Herotech1105/Anwendungsprojekt.Inf/documentation/Phase_4/API_Phase_4_Lennart_Esch.pdf

# Phase 4

# Storing Censor Data in Database (Lennart Esch)

Barnabas Steiner - Benjamin Hager - Jannis Weber - Lennart Esch - Tim Dorozynski - Walter Neer

# Agenda

# 1. Problemstellung 2. Deployment 3. Aufgaben 4. Controller 5. NGINX 6. WebServer 7. MariaDB 8. Zusammenspiel

# Problemstellung

# - Datentransfer

# - MQTT-Broker -> Datenbank - Sichere Übertragung

# - Kommunikation

# - PICO <-> Controller

# Deployment

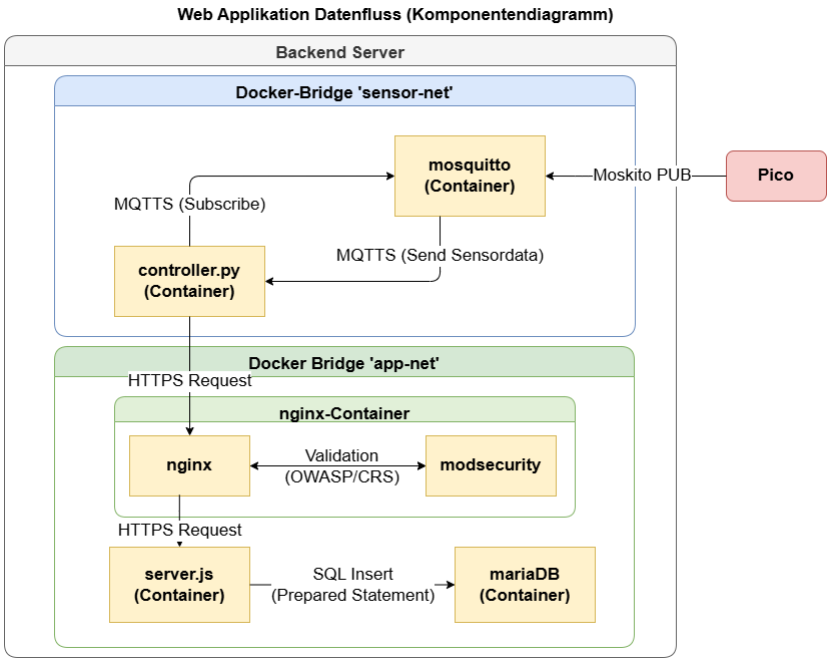
[picture p68: figure]

# Deployment

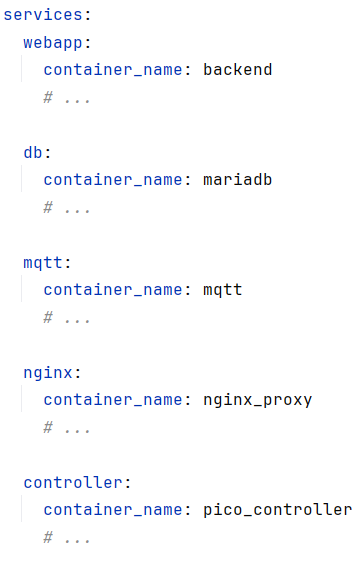
[picture p69: figure]

# - Mittels docker-compose.yml

# Aufgaben


# Controller

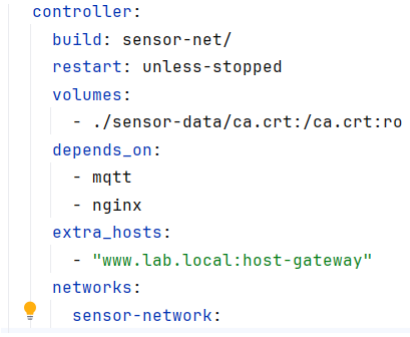
[picture p70: figure]

# - Python Script - Image gebaut durch Dockerfile - Dateizugriff auf Zertifikat - HTTPS Zugriff auf host-system

# Controller

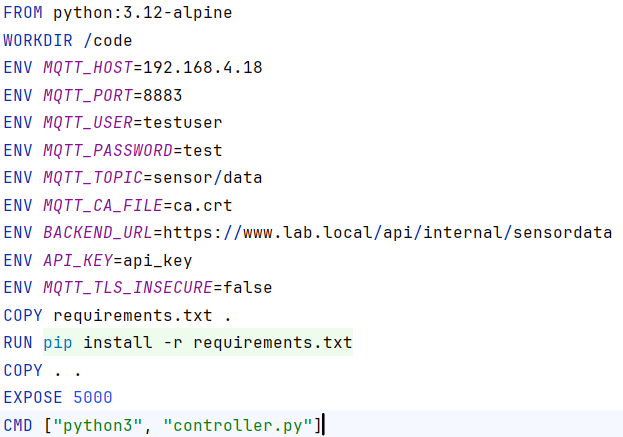
[picture p71: figure]

# - Basierend auf Python 3.12 Image - Umgebungsvariablen für das Skript - Installation aus requirements.txt

# - Paho_mqtt - Requests

# Controller

# - Client aus paho_mqtt

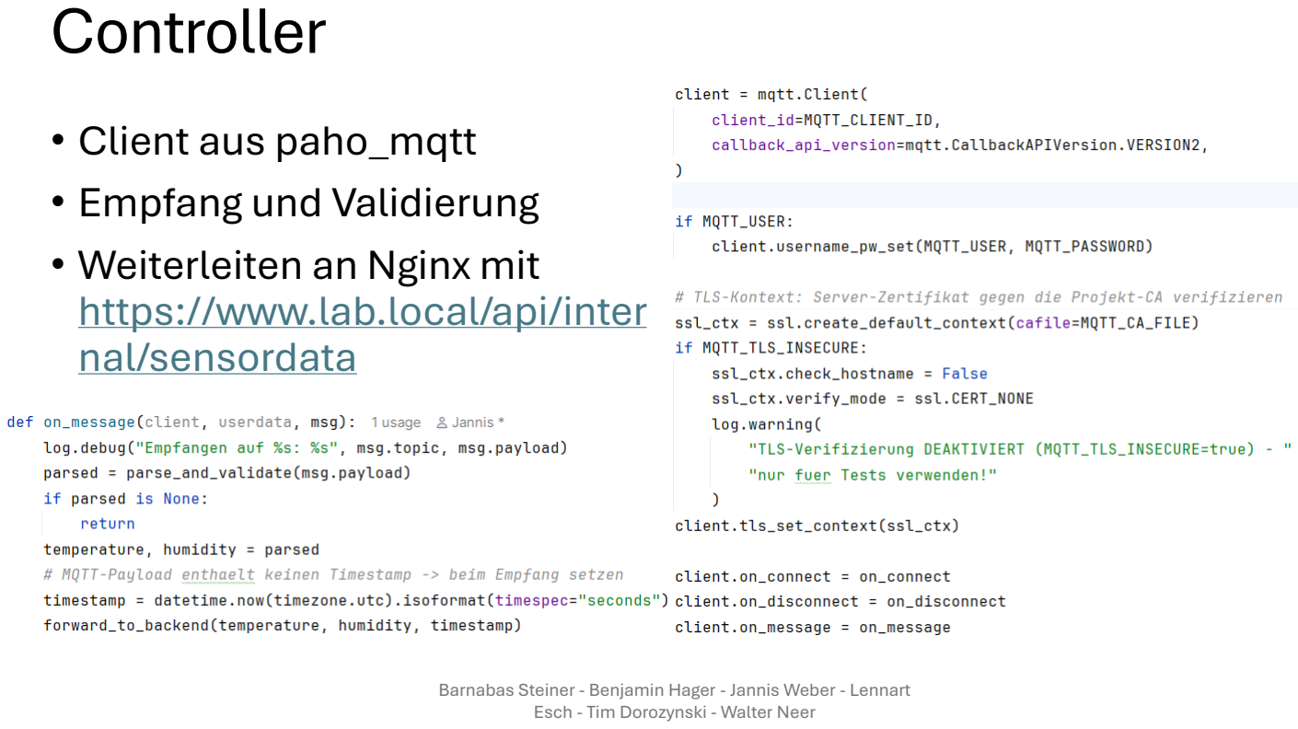
[picture p72: page 9]

# - Empfang und Validierung - Weiterleiten an Nginx mit https://www.lab.local/api/inter nal/sensordata (https://www.lab.local/api/internal/sensordata)

# Nginx

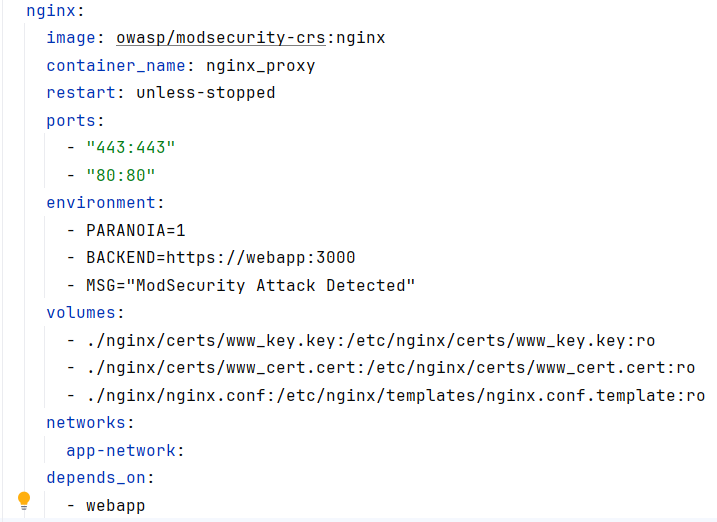
[picture p73: figure]

# - OWASP-Image

# - SQL Injection - XSS - Directory Traversal

# - HTTP/HTTPS Ports geöffnet - Niedrige Sicherheitsstufe - Zugriff auf Zertifikate

# Nginx

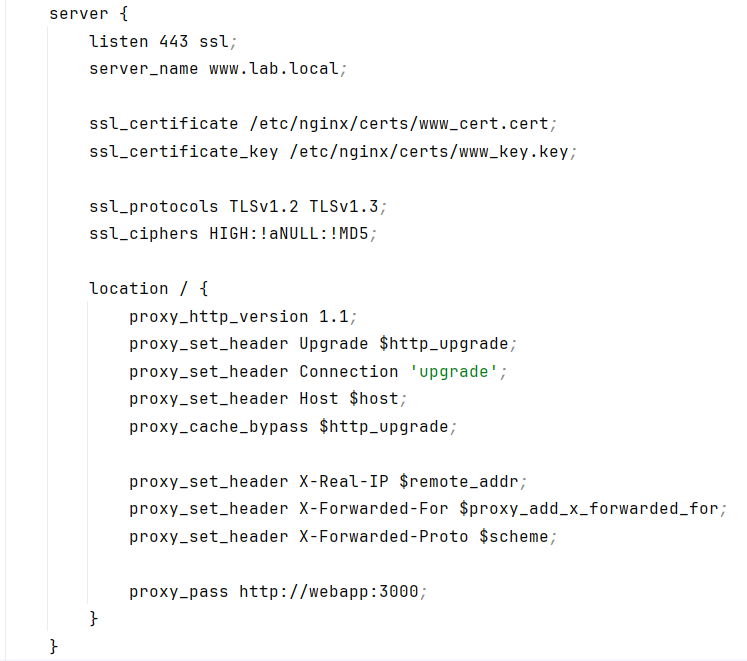
[picture p74: figure]

# - HTTPS Weiterleitung auf webapp - Selbsterstellte Zertifikate

# Webserver

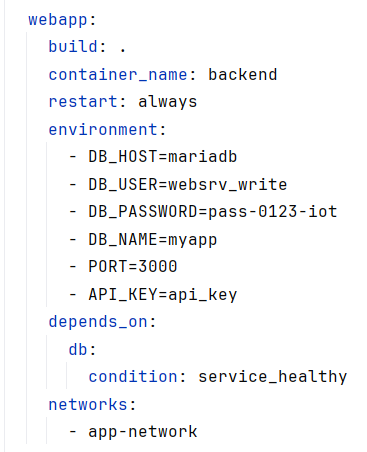
[picture p75: figure]

# - Node/Express server - Image gebaut aus Dockerfile - Datenbank Credentials - Api-Key

# Webserver

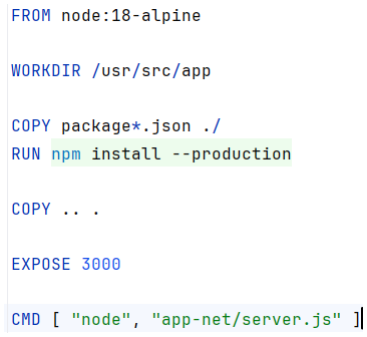
[picture p76: figure]

# - Basiert auf Node-Image - Installiert mit package.json

# - Express - Dotenv - MariaDB

# - Läuft intern auf 3000

# Webserver

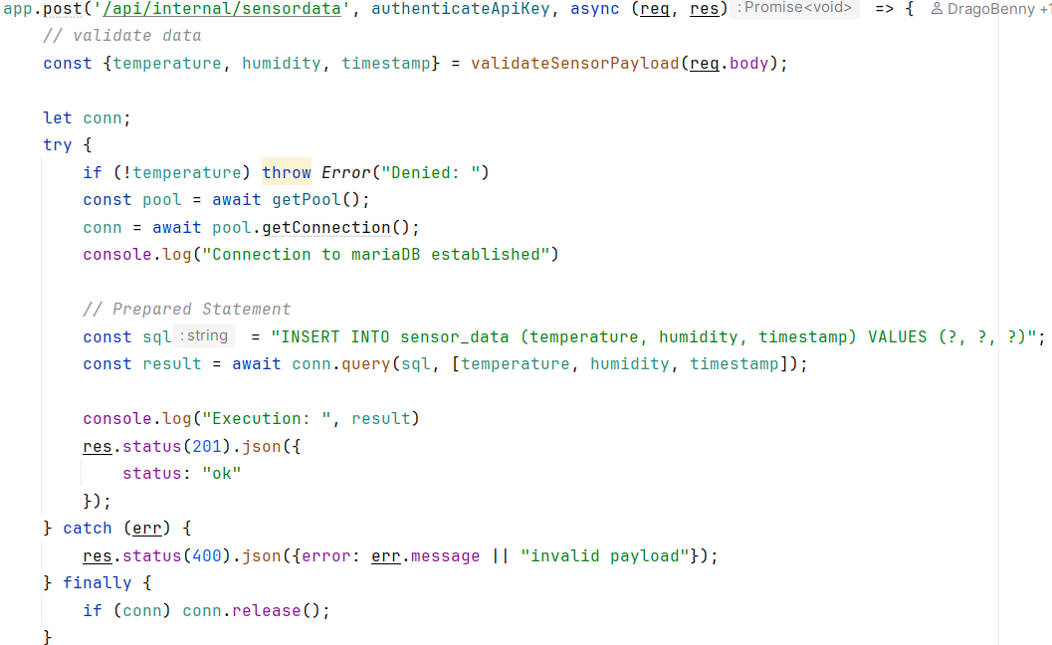
[picture p77: figure]

# MariaDB

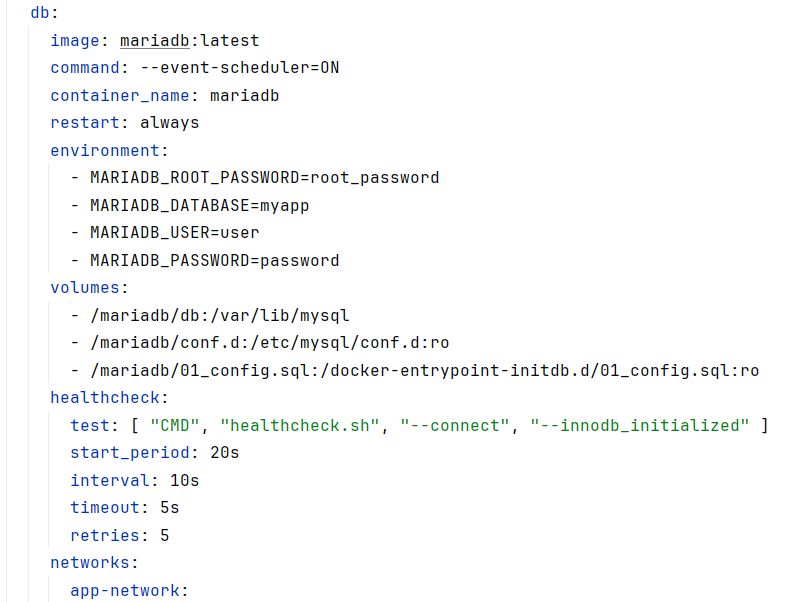
[picture p78: figure]

# - Event Scheduler - Credentials - Persistenz - Healthcheck

# MariaDB

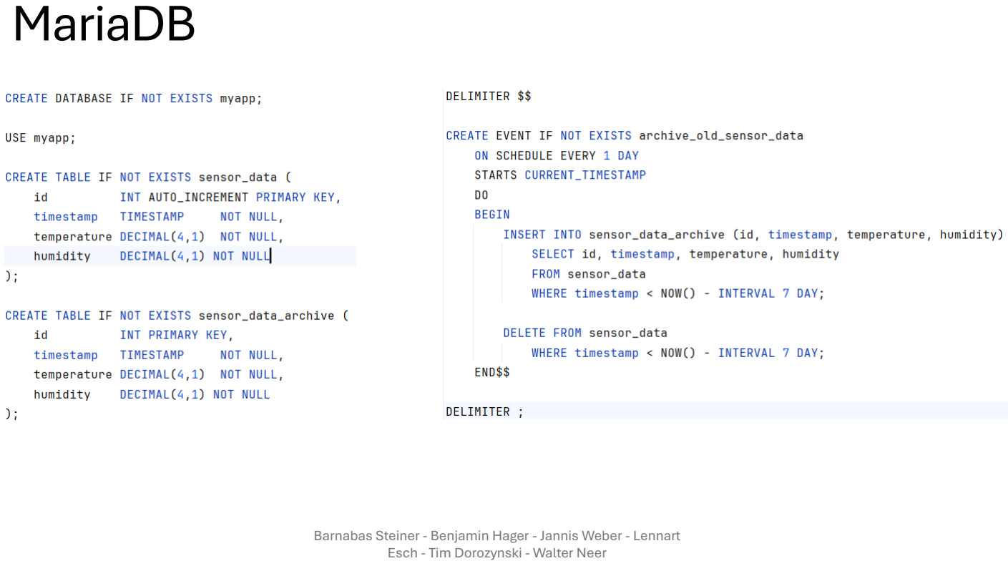
[picture p79: page 16]

# Zusammenspiel

# - E2E Test

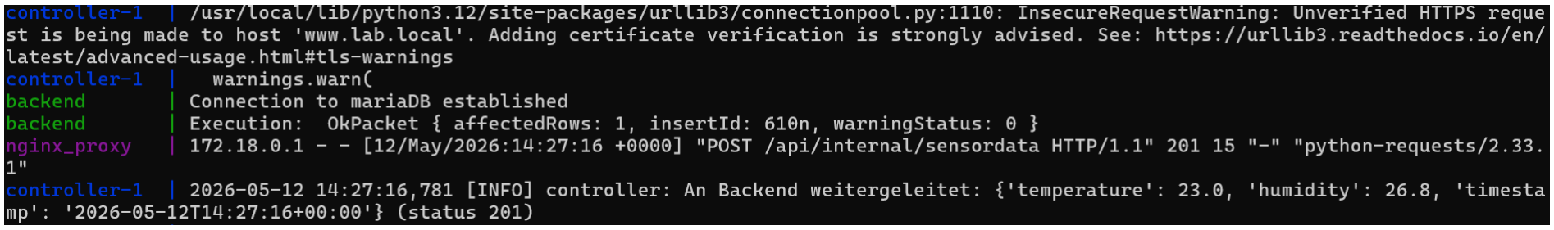
[picture p80: figure]

# - Warnung Zertifikat Nginx - Datenbank Query Ausführung - Response Code 201 an Controller

# Zusammenspiel

# - Verbindung mit MariaDB

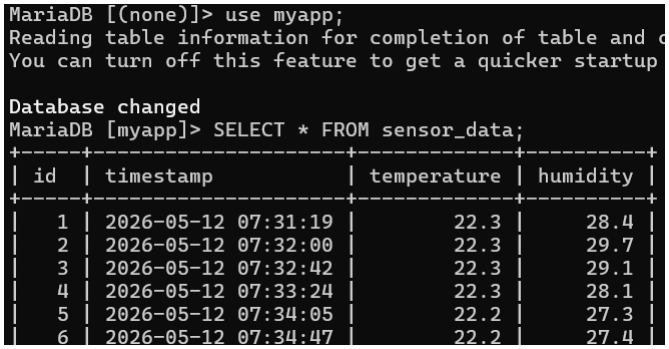
[picture p81: figure]

# - Database myapp - Sensor Data wird gefüllt

# Vielen Dank für Ihre Aufmerksamkeit
