Herotech1105/Anwendungsprojekt.Inf/documentation/Phase_1/Gantt_Phase1.pdf

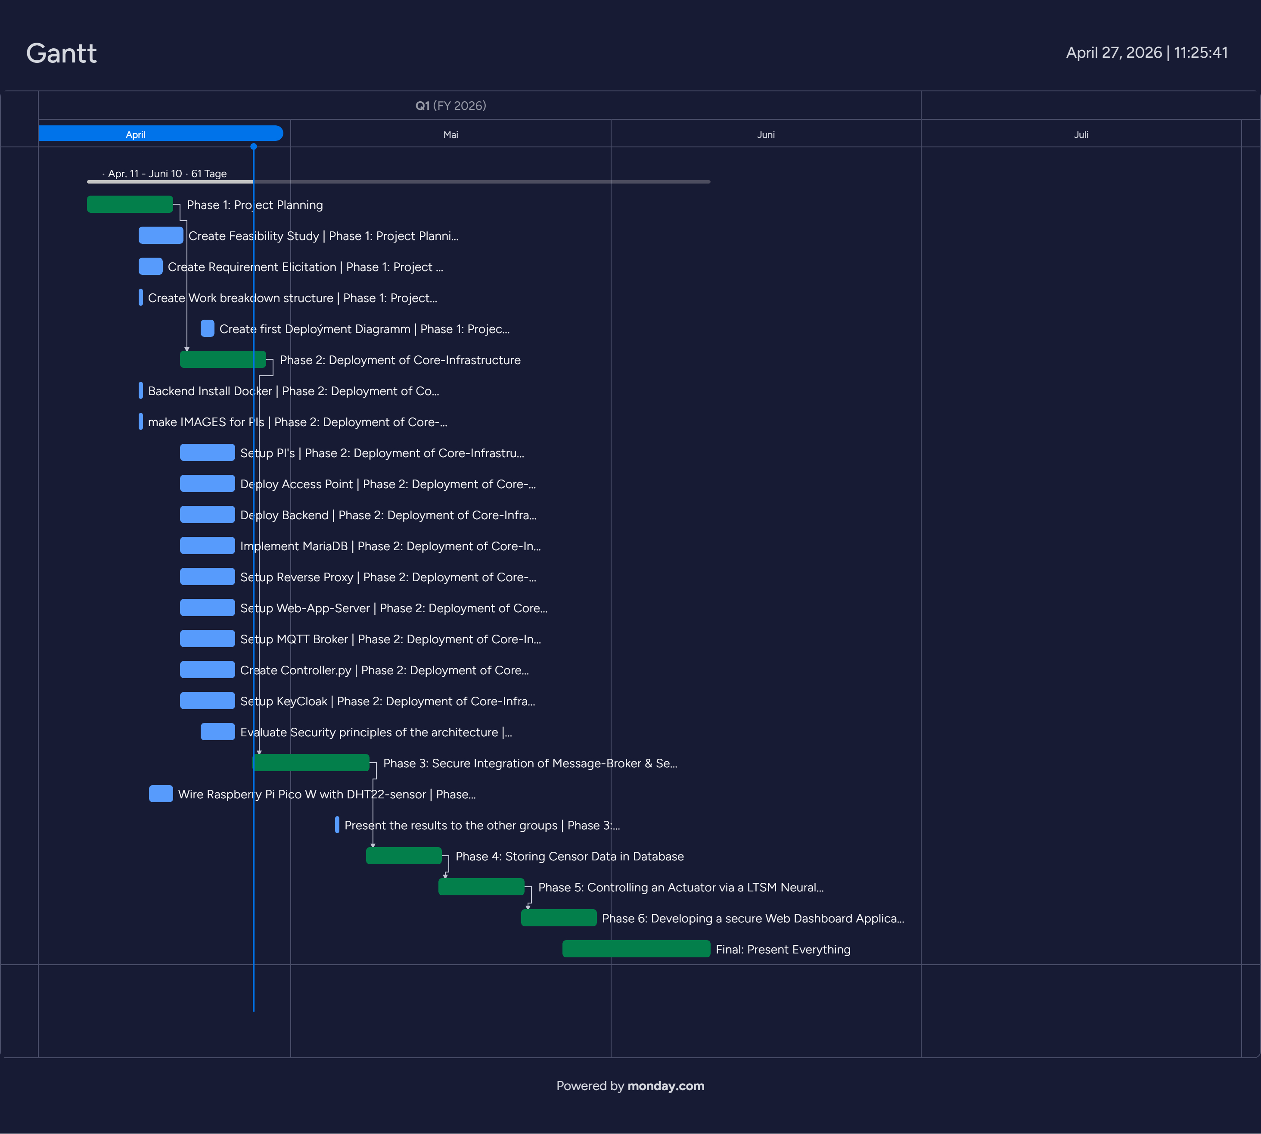
[picture p82: page 1]
