Herotech1105/Anwendungsprojekt.Inf/documentation/pico exterior/IMG_20260610_142606209.jpg

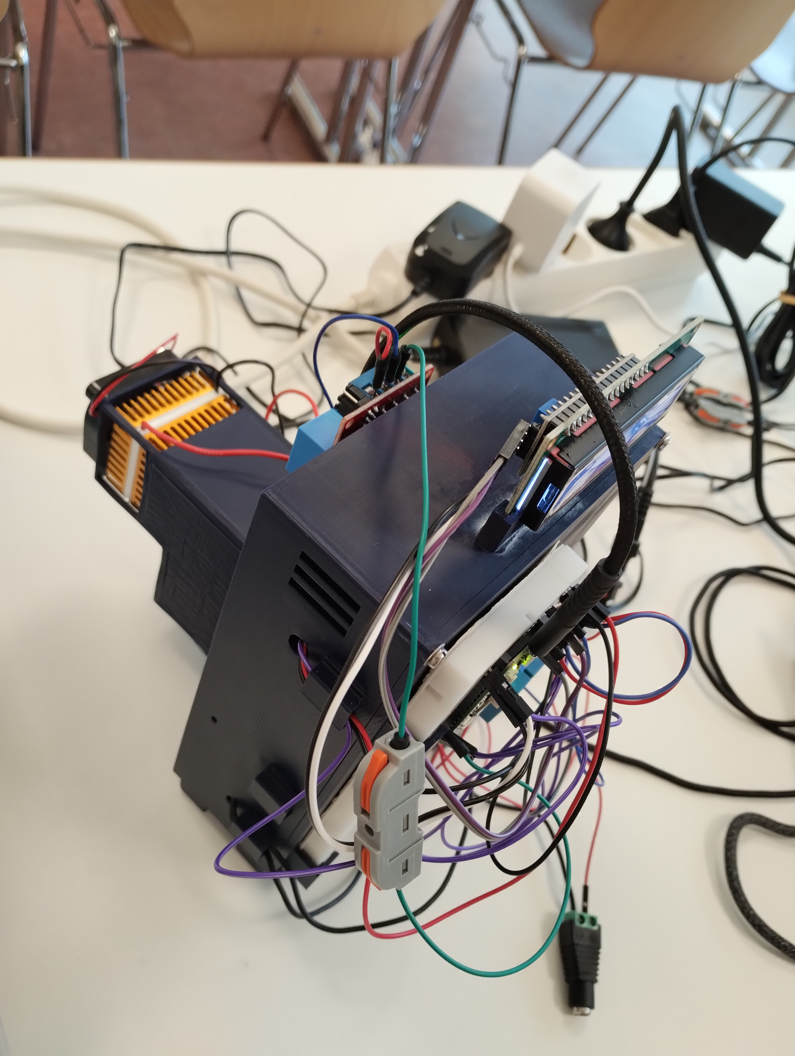
documentation/pico exterior/IMG_20260610_142606209.jpg
